davidhernandez0771/Shellhacks-2026-Project---COOP/docs/screenshots/dashboard-390-live.jpg

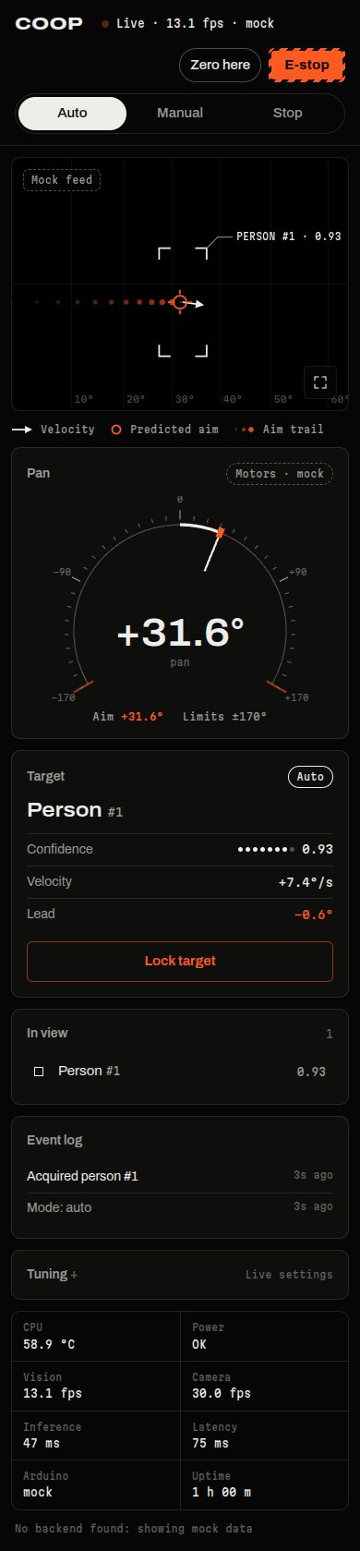
docs/screenshots/dashboard-390-live.jpg
