davidhernandez0771/Shellhacks-2026-Project---COOP/docs/screenshots/dashboard-1440-hot.jpg

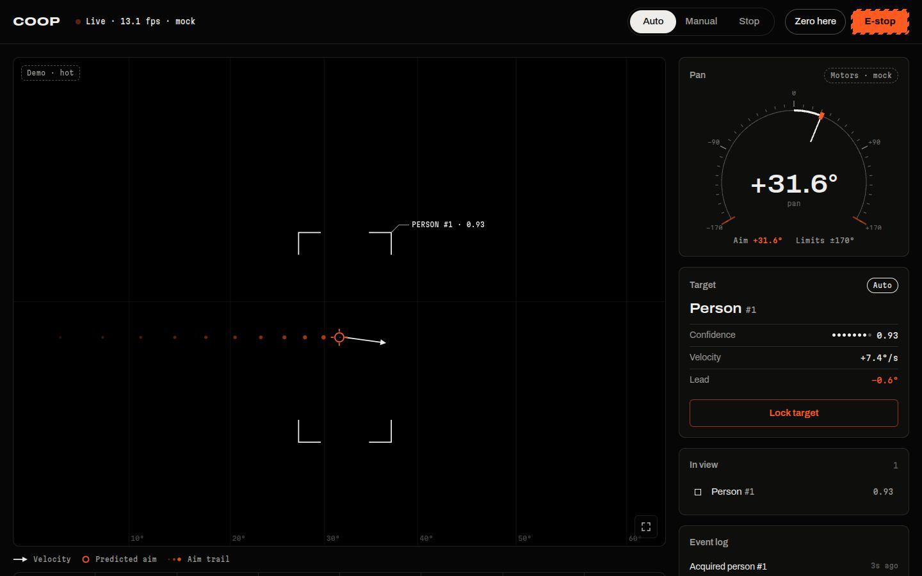
docs/screenshots/dashboard-1440-hot.jpg
