davidhernandez0771/Shellhacks-2026-Project---COOP/docs/screenshots/site-390-00-loader.jpg

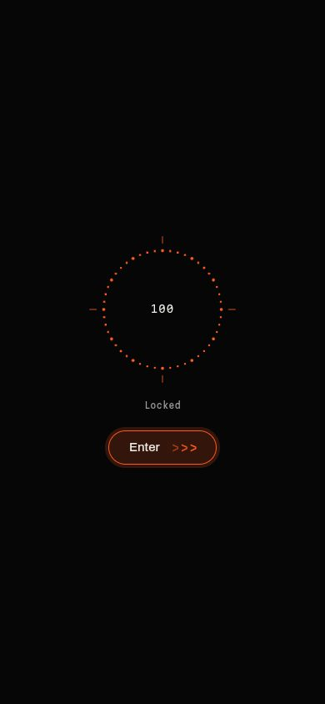
docs/screenshots/site-390-00-loader.jpg
