davidhernandez0771/Shellhacks-2026-Project---COOP/docs/screenshots/site-390-01-intro-decode.jpg

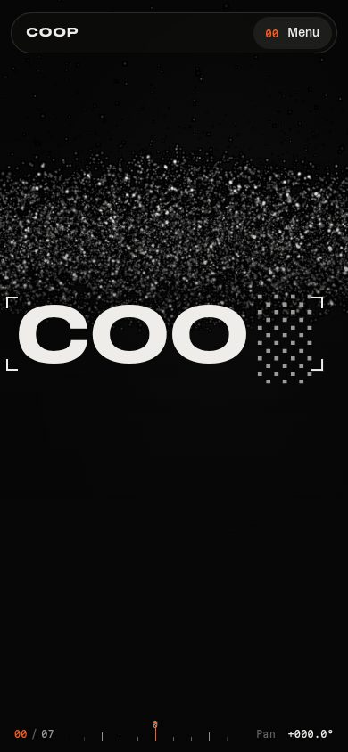
docs/screenshots/site-390-01-intro-decode.jpg
