davidhernandez0771/Shellhacks-2026-Project---COOP/docs/screenshots/site-390-02-intro.jpg

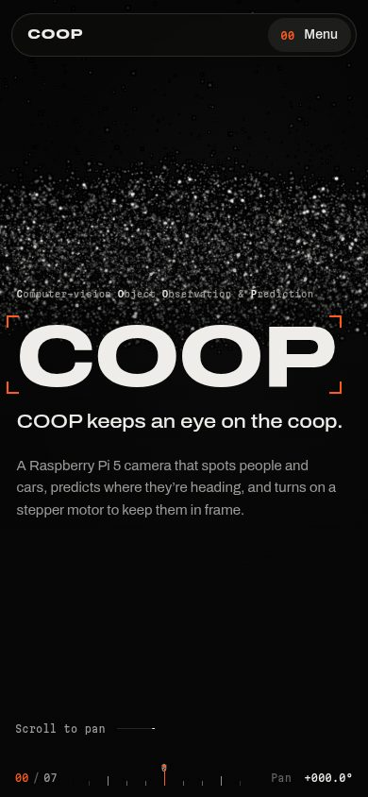
docs/screenshots/site-390-02-intro.jpg
