davidhernandez0771/Shellhacks-2026-Project---COOP/docs/screenshots/site-390-03-see.jpg

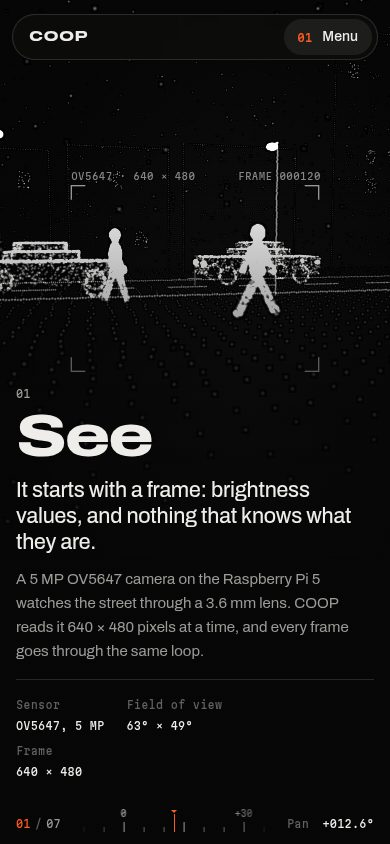
docs/screenshots/site-390-03-see.jpg
