davidhernandez0771/Shellhacks-2026-Project---COOP/docs/screenshots/site-390-04-detect.jpg

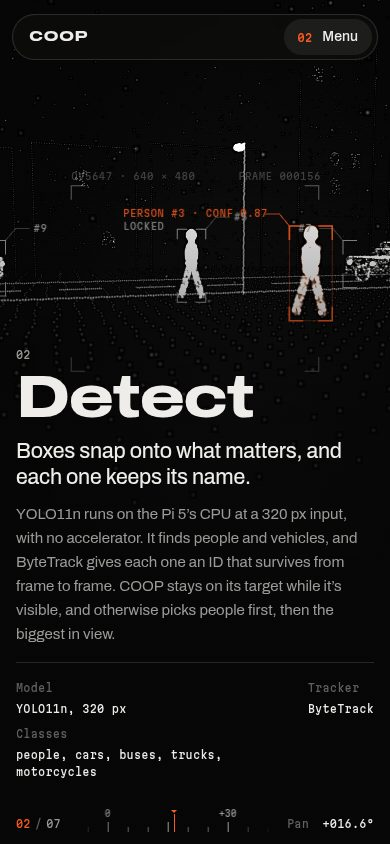
docs/screenshots/site-390-04-detect.jpg
