davidhernandez0771/Shellhacks-2026-Project---COOP/docs/screenshots/site-390-05-predict.jpg

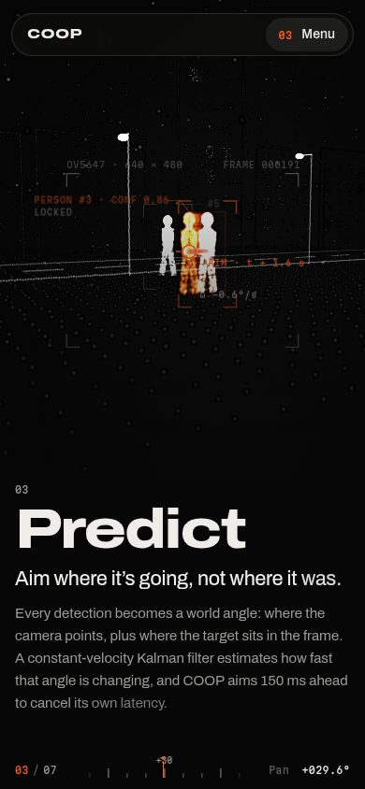
docs/screenshots/site-390-05-predict.jpg
