davidhernandez0771/Shellhacks-2026-Project---COOP/docs/screenshots/site-390-06-predict.jpg

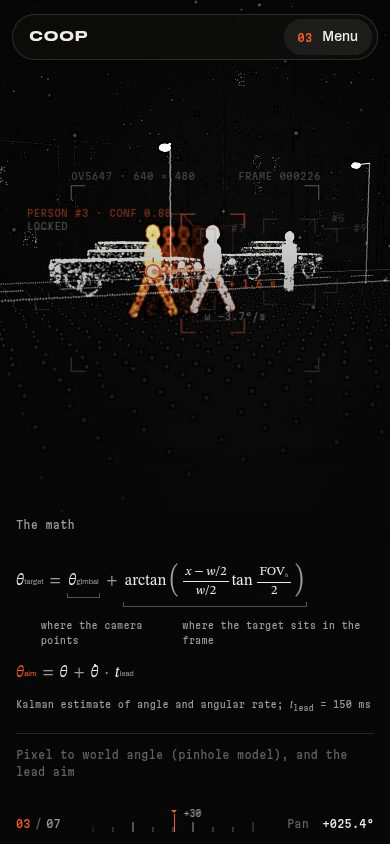
docs/screenshots/site-390-06-predict.jpg
