davidhernandez0771/Shellhacks-2026-Project---COOP/docs/screenshots/site-390-10-team.jpg

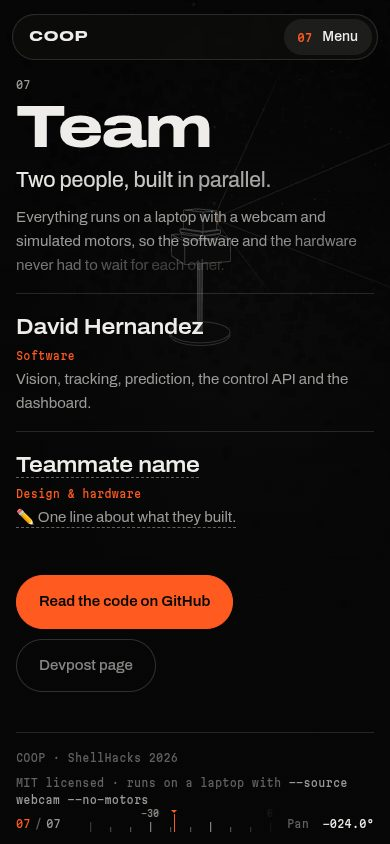
docs/screenshots/site-390-10-team.jpg
