davidhernandez0771/Shellhacks-2026-Project---COOP/docs/screenshots/site-1440-00-loader.jpg

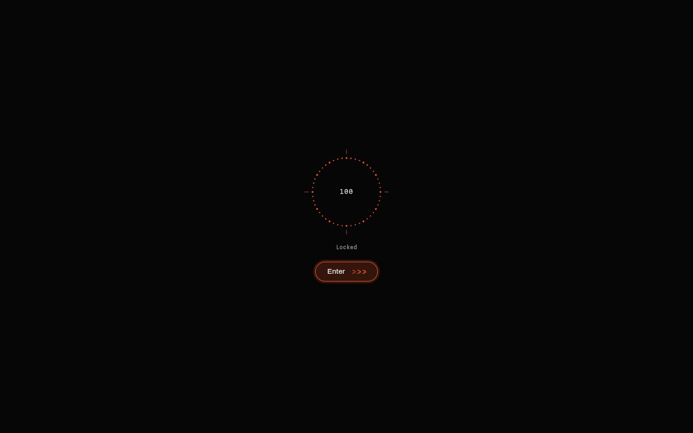
docs/screenshots/site-1440-00-loader.jpg
