davidhernandez0771/Shellhacks-2026-Project---COOP/docs/screenshots/site-1440-01-intro-decode.jpg

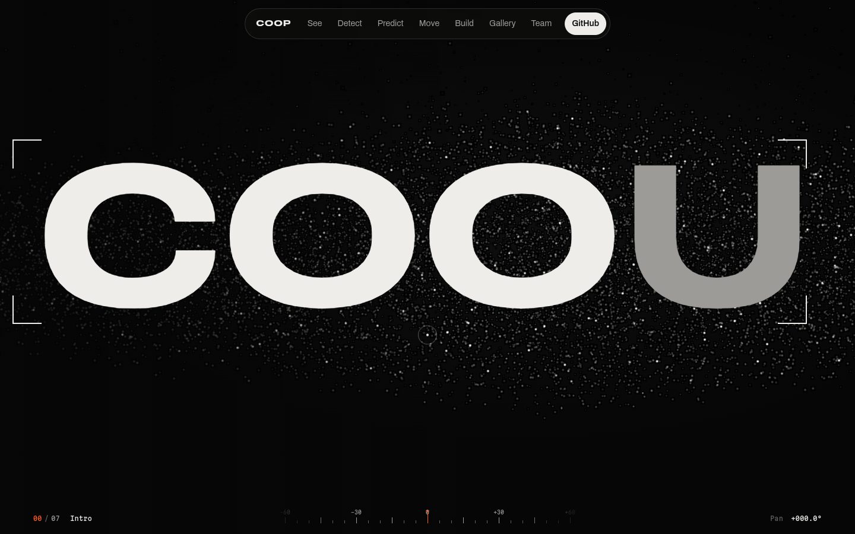
docs/screenshots/site-1440-01-intro-decode.jpg
