davidhernandez0771/Shellhacks-2026-Project---COOP/docs/screenshots/site-1440-04-detect.jpg

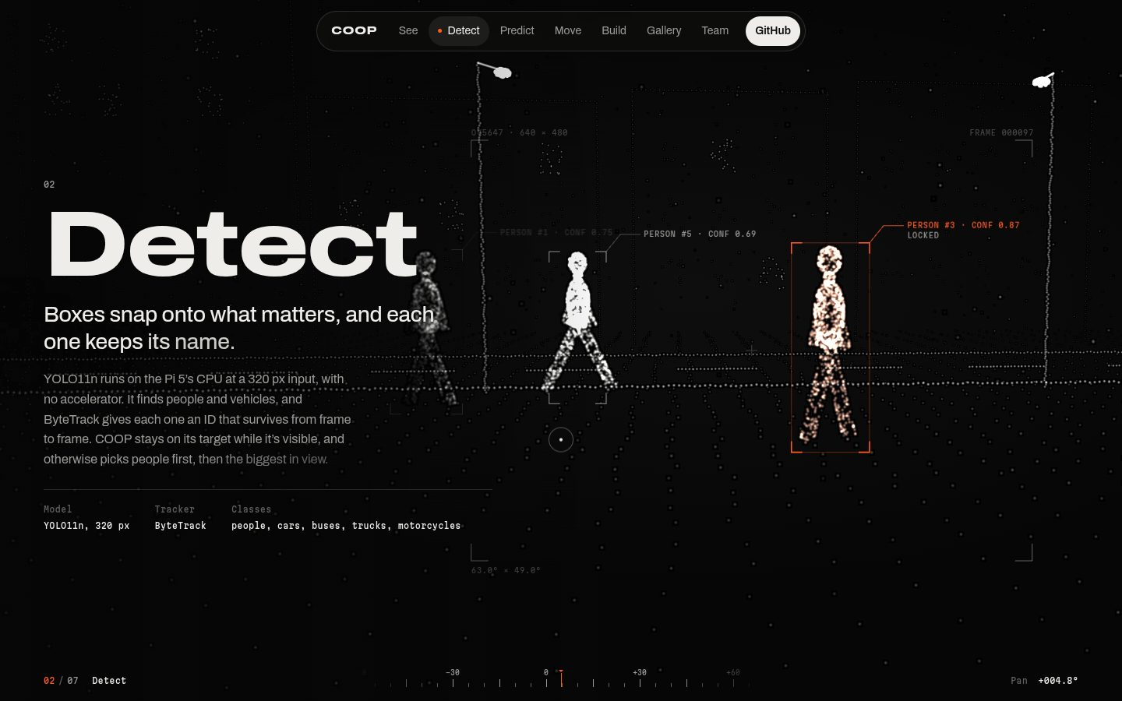
docs/screenshots/site-1440-04-detect.jpg
