davidhernandez0771/Shellhacks-2026-Project---COOP/site/media/gallery/02-cad-camera-mount-card.jpg

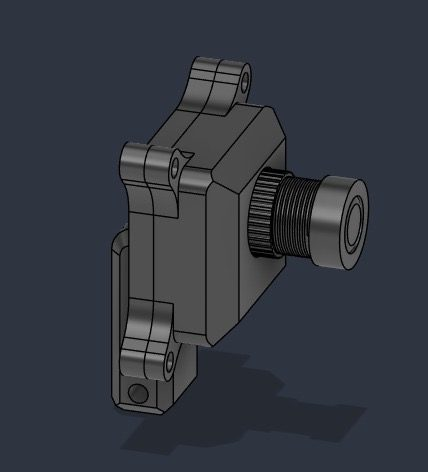
site/media/gallery/02-cad-camera-mount-card.jpg
