davidhernandez0771/Shellhacks-2026-Project---COOP/site/media/gallery/03-cad-pi-in-case-card.jpg

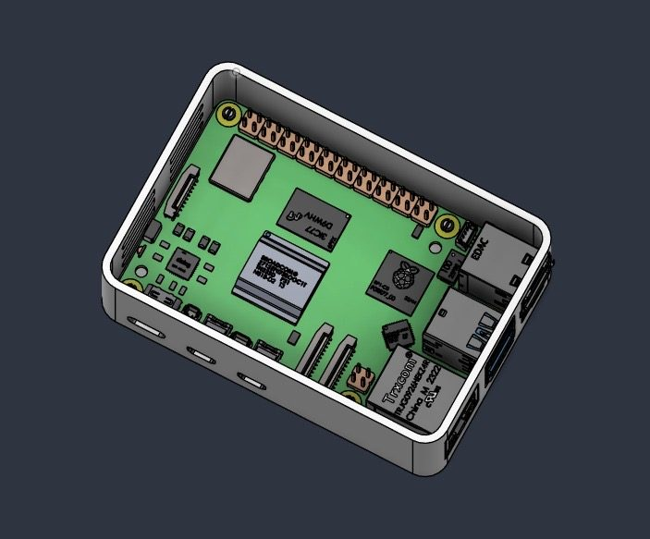
site/media/gallery/03-cad-pi-in-case-card.jpg
