davidhernandez0771/Shellhacks-2026-Project---COOP/site/media/gallery/06-case-side-ports-card.jpg

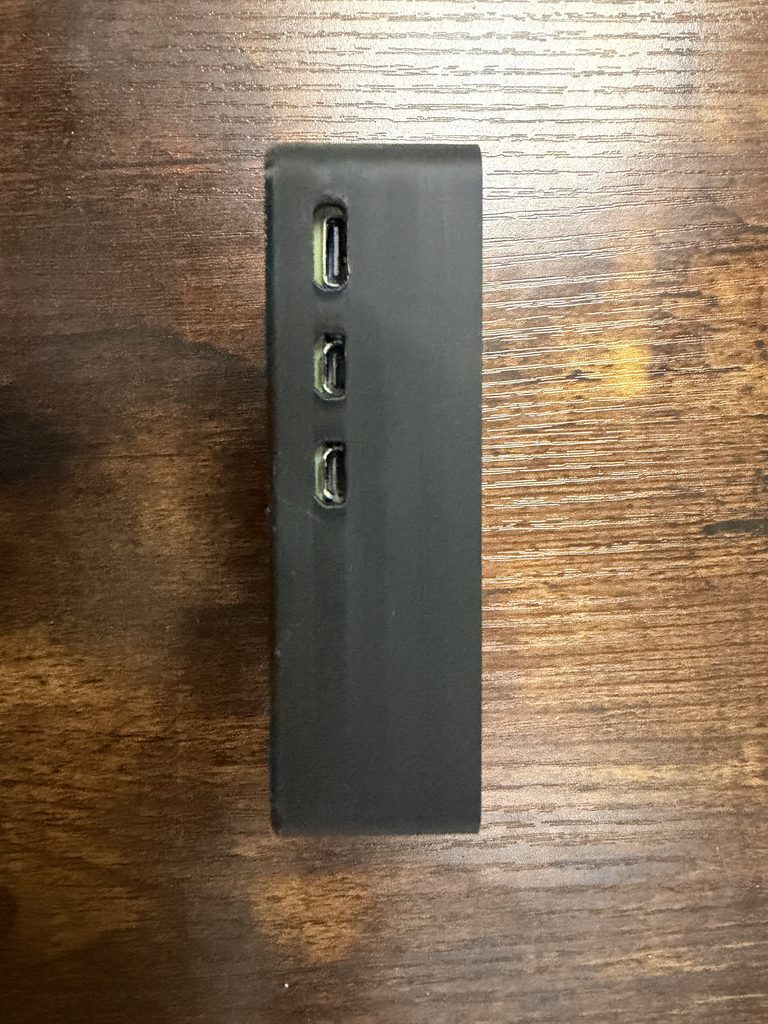
site/media/gallery/06-case-side-ports-card.jpg
