davidhernandez0771/Shellhacks-2026-Project---COOP/site/media/gallery/07-case-front-ports-card.jpg

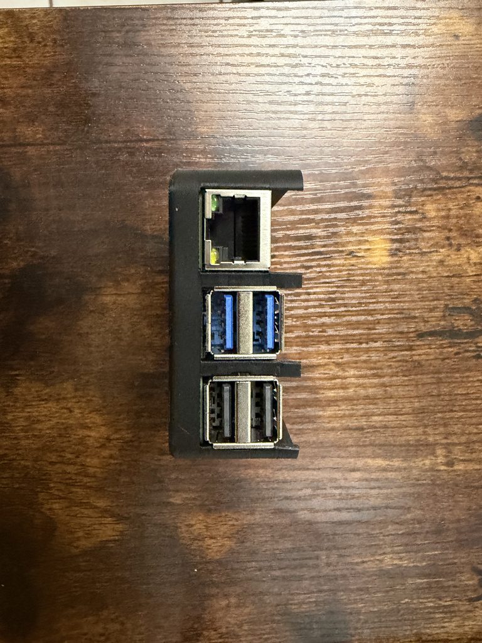
site/media/gallery/07-case-front-ports-card.jpg
