davidhernandez0771/Shellhacks-2026-Project---COOP/site/media/gallery/08-case-vents-card.jpg

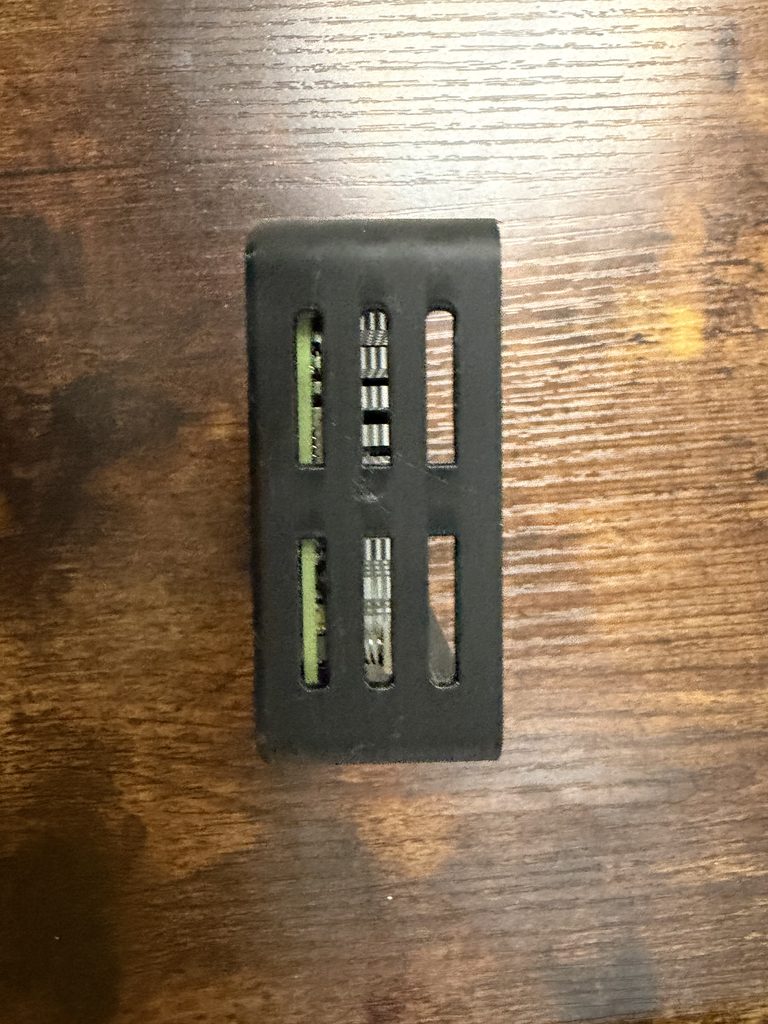
site/media/gallery/08-case-vents-card.jpg
