davidhernandez0771/Shellhacks-2026-Project---COOP/site/media/gallery/10-camera-mounted-card.jpg

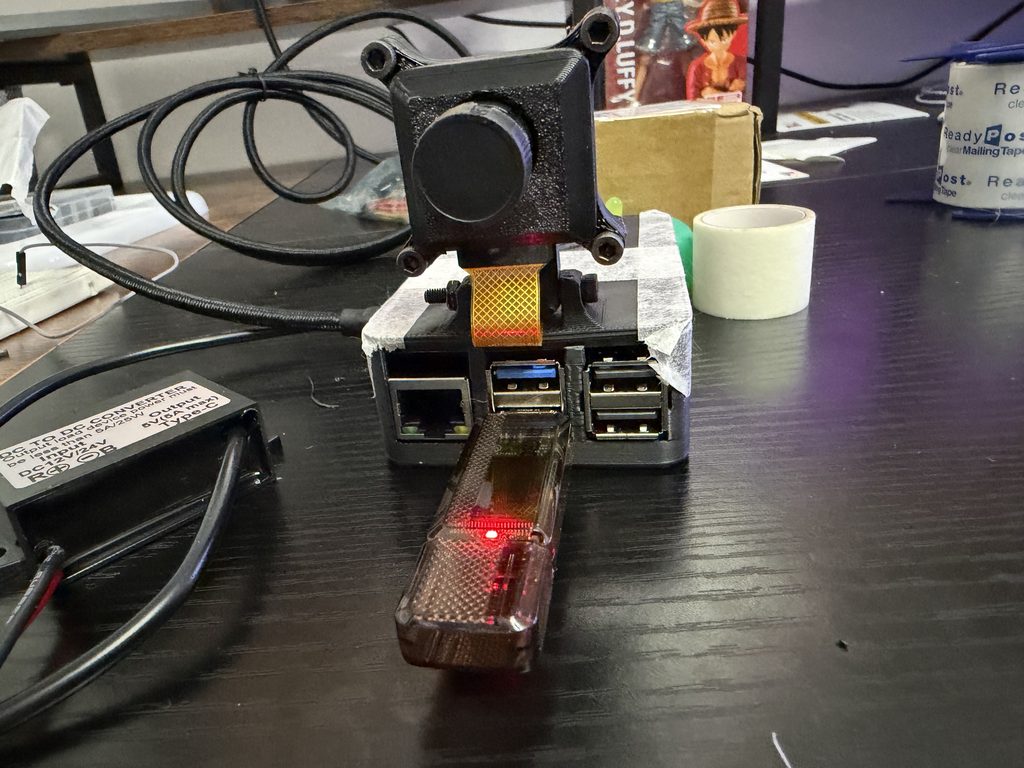
site/media/gallery/10-camera-mounted-card.jpg
