davidhernandez0771/Shellhacks-2026-Project---COOP/docs/screenshots/site-1440-08-build.jpg

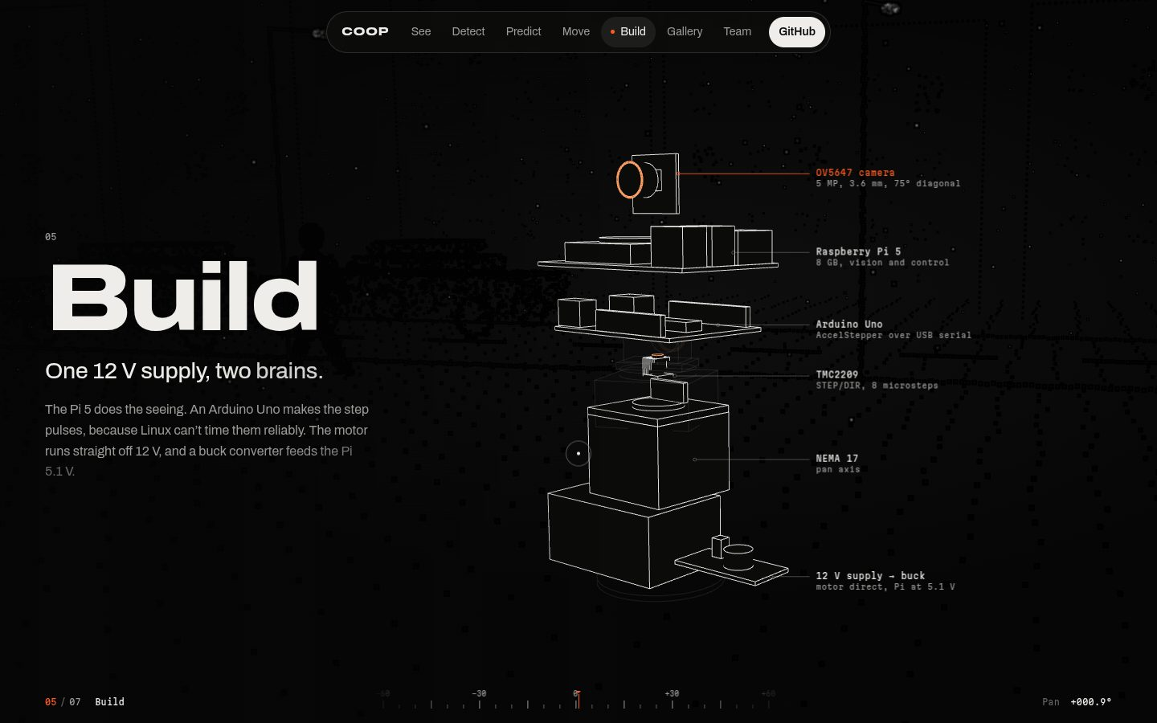
docs/screenshots/site-1440-08-build.jpg
