davidhernandez0771/Shellhacks-2026-Project---COOP/site/media/gallery/11-test-danger-1-card.jpg

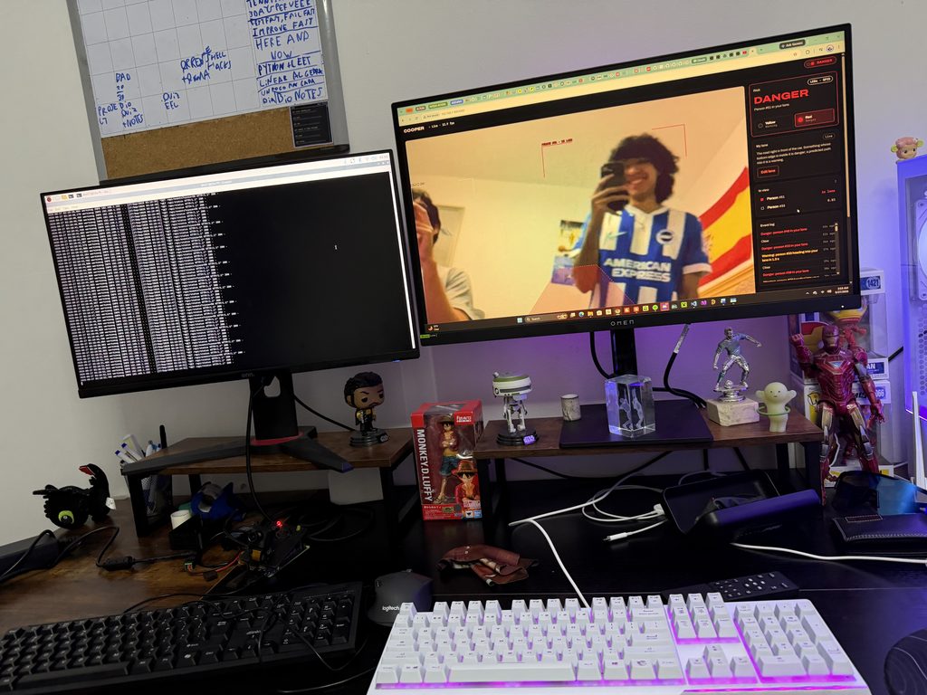
site/media/gallery/11-test-danger-1-card.jpg
